fuwei007/NavBot-EG02/1-3D Files/1.jpg

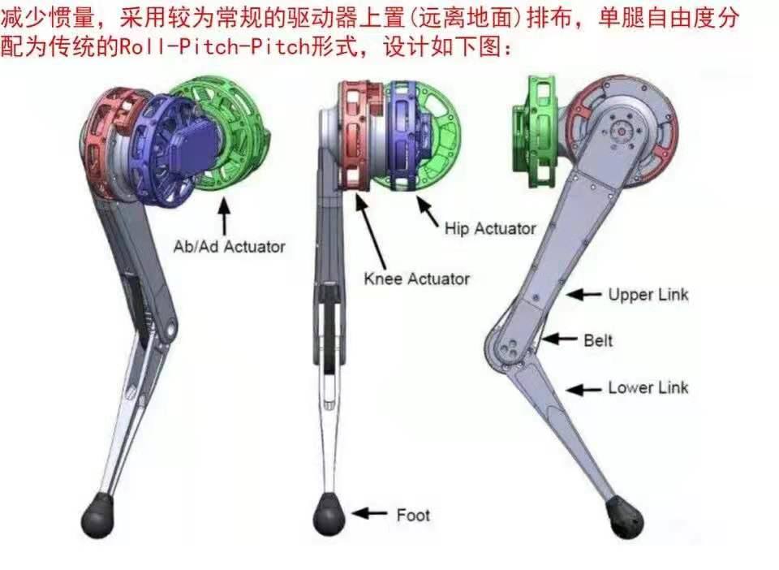
1-3D Files/1.jpg
