fuwei007/NavBot-EG02/1-3D Files/sw2022/MIT-机器狗-旋转关节.SLDASM

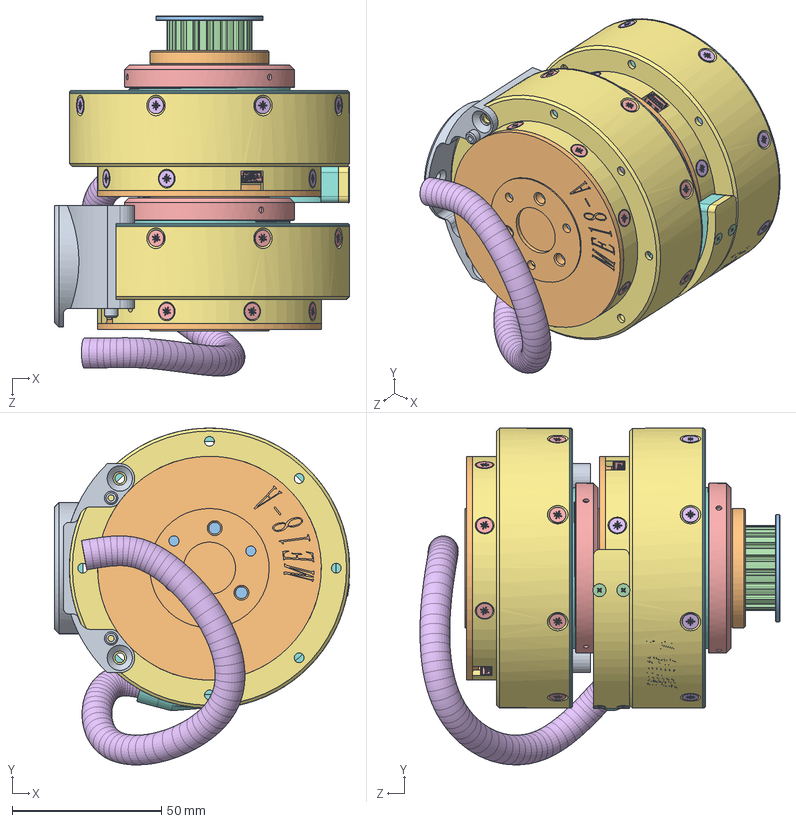
[picture p11: CAD file, 2025-09-24]
1-3D Files/sw2022/MIT-机器狗-旋转关节.SLDASM
99.0 x 112.9 x 120.7 mm
Smart Engines.sldasm-Part-1
Smart Engines.sldasm-Part-2 x 3
Smart Engines.sldasm-Part-4 x 2
Smart Engines.sldasm-Part-5 x 4
Smart Engines.sldasm-Part-6 x 13
Smart Engines.sldasm-Part-7
Smart Engines.sldasm-Part-8
Smart Engines.sldasm-Part-9 x 6
Smart Engines.sldasm-Part-10 x 2
3_BODY
Smart Engines.sldasm-Part-11 x 2
Smart Engines.sldasm-Part-12 x 2
Smart Engines.sldasm-Part-13 x 2
Smart Engines.sldasm-Part-14 x 2
Smart Engines.sldasm-Part-15 x 2
Smart Engines.sldasm-Part-16 x 2
Smart Engines.sldasm-Part-95
Smart Engines.sldasm-Part-96
GEAR_2_BODY
Smart Engines.sldasm-Part-105 x 13
Smart Engines.sldasm-Part-110
Smart Engines.sldasm-Part-114 x 2
Smart Engines.sldasm-Part-115 x 2
Smart Engines.sldasm-Part-116 x 2
Smart Engines.sldasm-Part-117 x 2
Smart Engines.sldasm-Part-118 x 2
Smart Engines.sldasm-Part-119 x 2
Smart Engines.sldasm-Part-120 x 2
Smart Engines.sldasm-Part-121 x 2
Smart Engines.sldasm-Part-122 x 2
