fuwei007/NavBot-EG02/1-3D Files/sw2022/Smart Engines.sldasm-Part-19.SLDPRT

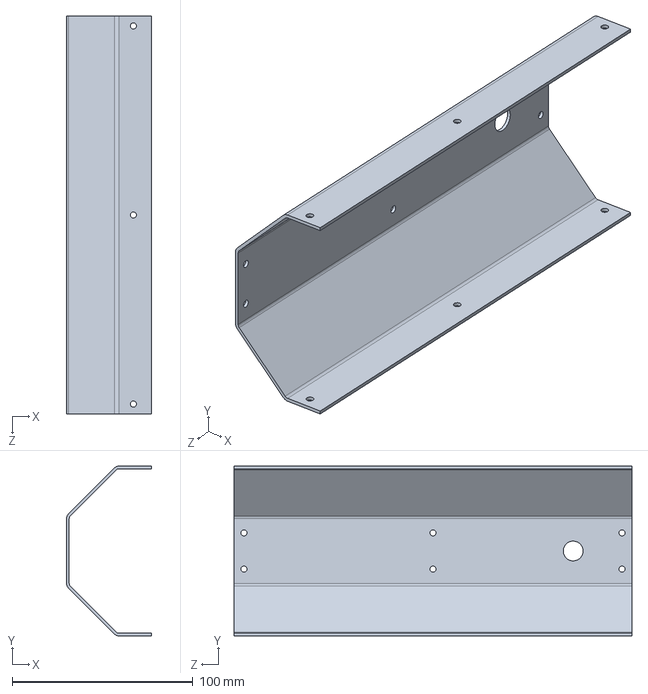
[picture p12: CAD file, 2025-09-24]
1-3D Files/sw2022/Smart Engines.sldasm-Part-19.SLDPRT
47.0 x 93.9 x 220.0 mm
