fuwei007/NavBot-EG02/1-3D Files/sw2022/MIT-机器狗-身体部分.SLDASM

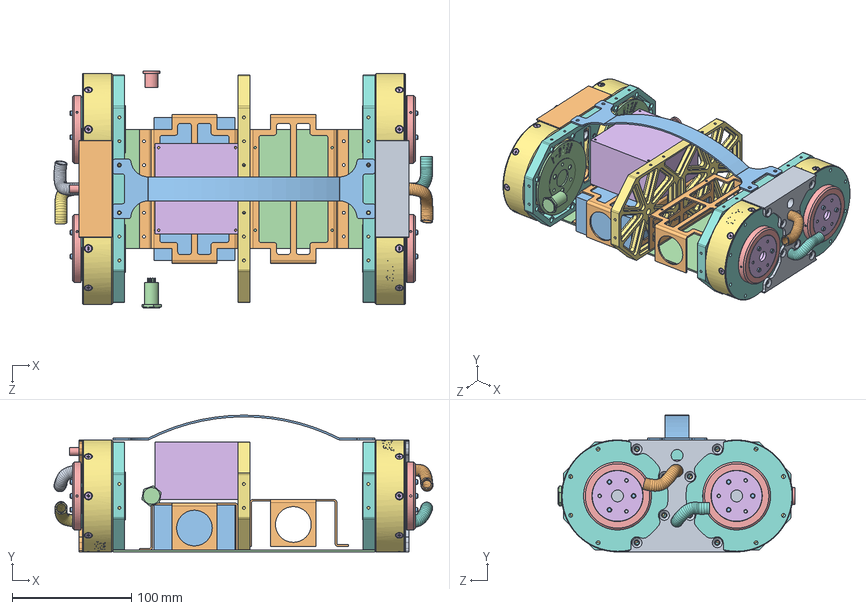
[picture p13: CAD file, 2025-09-24]
1-3D Files/sw2022/MIT-机器狗-身体部分.SLDASM
318.0 x 114.8 x 198.9 mm
Smart Engines.sldasm-Part-4 x 4
Smart Engines.sldasm-Part-9 x 12
Smart Engines.sldasm-Part-10 x 4
Smart Engines.sldasm-Part-12 x 4
Smart Engines.sldasm-Part-13 x 4
Smart Engines.sldasm-Part-14 x 4
Smart Engines.sldasm-Part-15 x 4
Smart Engines.sldasm-Part-16 x 4
Smart Engines.sldasm-Part-17 x 2
Smart Engines.sldasm-Part-18
Smart Engines.sldasm-Part-21
Smart Engines.sldasm-Part-22
Smart Engines.sldasm-Part-23
Smart Engines.sldasm-Part-24
Smart Engines.sldasm-Part-25 x 2
Smart Engines.sldasm-Part-26
Smart Engines.sldasm-Part-27
Smart Engines.sldasm-Part-28
Smart Engines.sldasm-Part-29
Smart Engines.sldasm-Part-30
Smart Engines.sldasm-Part-105 x 52
Smart Engines.sldasm-Part-107
Smart Engines.sldasm-Part-109
Smart Engines.sldasm-Part-111
Smart Engines.sldasm-Part-113
Smart Engines.sldasm-Part-114 x 4
Smart Engines.sldasm-Part-115 x 4
Smart Engines.sldasm-Part-116 x 4
Smart Engines.sldasm-Part-117 x 4
Smart Engines.sldasm-Part-118 x 4
Smart Engines.sldasm-Part-119 x 4
Smart Engines.sldasm-Part-120 x 4
Smart Engines.sldasm-Part-121 x 4
Smart Engines.sldasm-Part-122 x 4
