fuwei007/NavBot-EG02/1-3D Files/sw2022/Smart Engines.sldasm-Part-120.SLDPRT

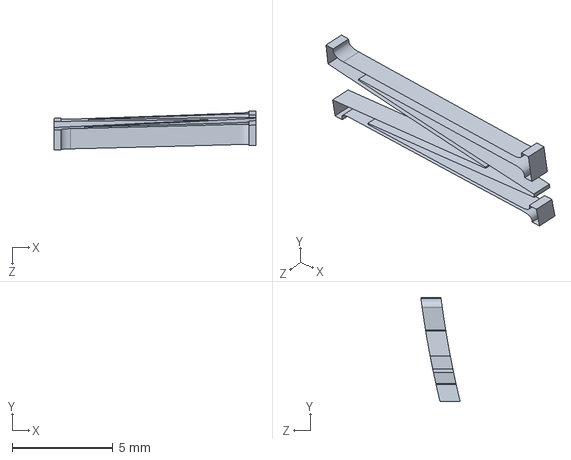
[picture p14: CAD file, 2025-09-24]
1-3D Files/sw2022/Smart Engines.sldasm-Part-120.SLDPRT
10.0 x 5.17 x 1.95 mm
