fuwei007/NavBot-EG02/3-Software/jetson_nano_-mit_-cheetah-main/resources/mini_body.obj

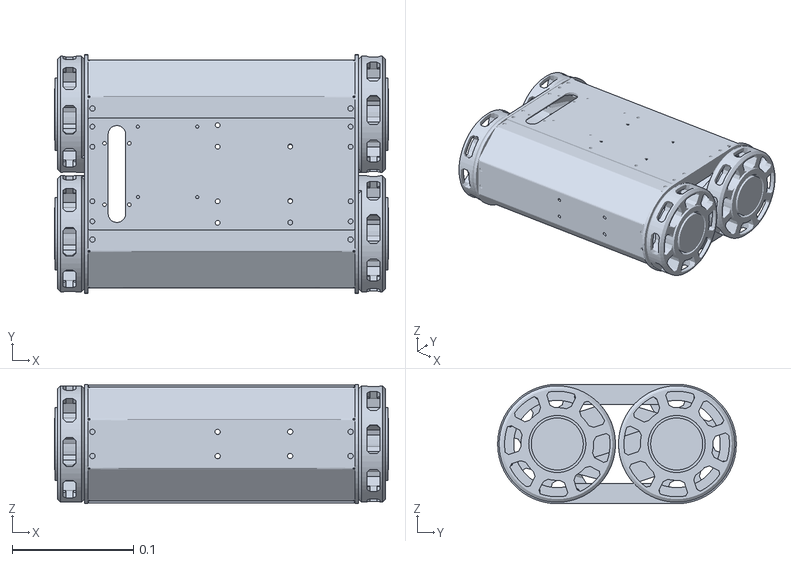
[picture p15: CAD file, 2025-09-24]
3-Software/jetson_nano_-mit_-cheetah-main/resources/mini_body.obj
0.275 x 0.197 x 0.0985
