fuwei007/NavBot-EG02/3-Software/jetson_nano_-mit_-cheetah-main/resources/sphere.obj

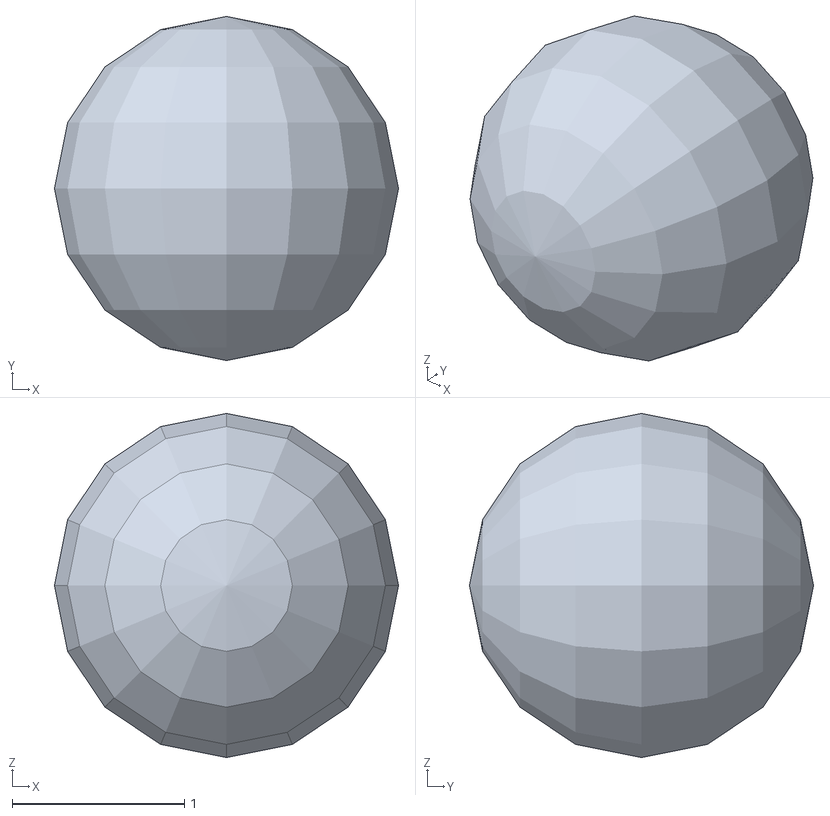
[picture p16: CAD file, 2025-09-24]
3-Software/jetson_nano_-mit_-cheetah-main/resources/sphere.obj
2.00 x 2.00 x 2.00
