fuwei007/NavBot-EG02/3-Software/jetson_nano_-mit_-cheetah-main/resources/mini_abad.obj

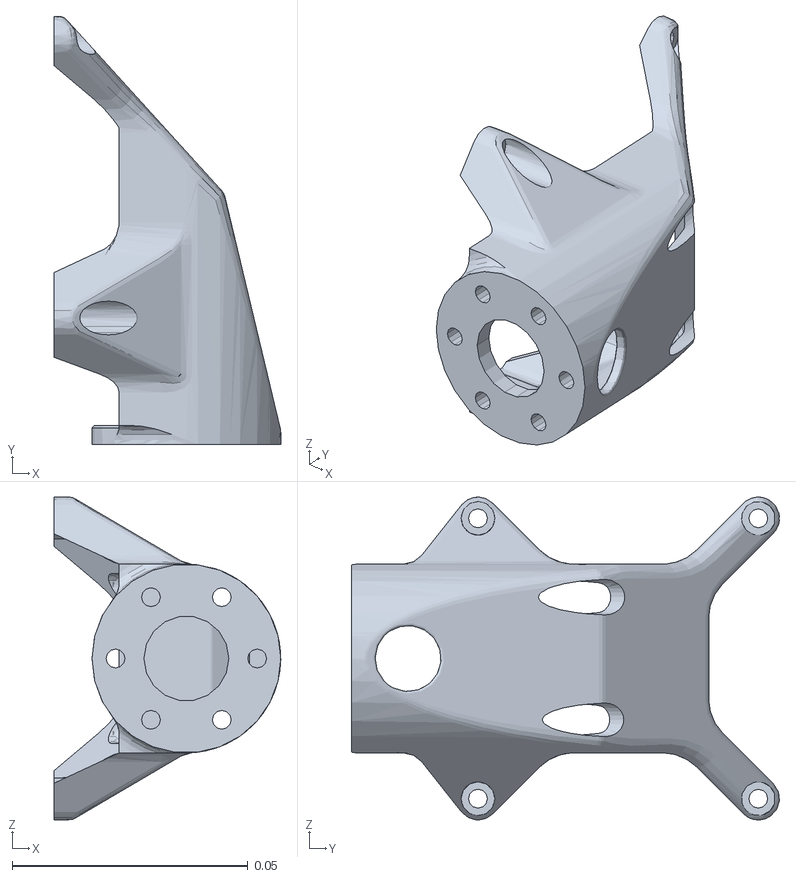
[picture p17: CAD file, 2025-09-24]
3-Software/jetson_nano_-mit_-cheetah-main/resources/mini_abad.obj
0.048 x 0.0907 x 0.0684
