fuwei007/NavBot-EG02/3-Software/jetson_nano_-mit_-cheetah-main/resources/mini_upper_link.obj

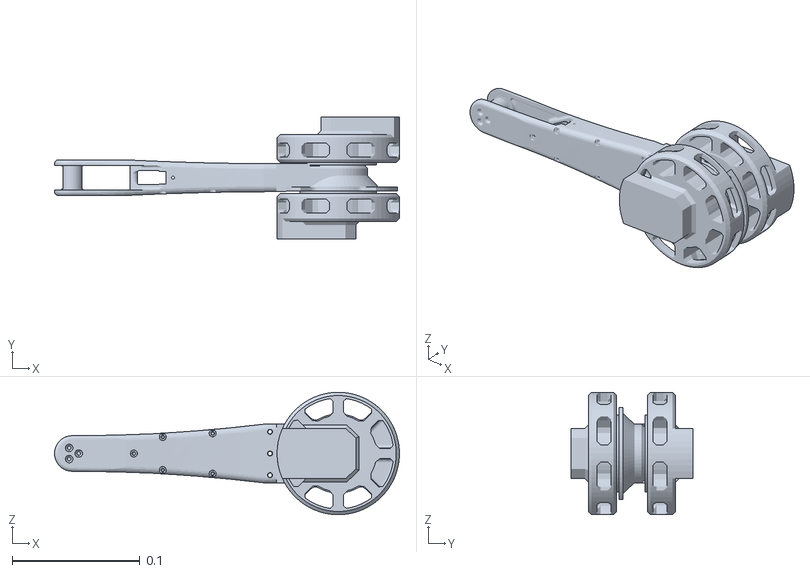
[picture p18: CAD file, 2025-09-24]
3-Software/jetson_nano_-mit_-cheetah-main/resources/mini_upper_link.obj
0.271 x 0.096 x 0.096
