fuwei007/NavBot-EG02/3-Software/jetson_nano_-mit_-cheetah-main/resources/c3_body.obj

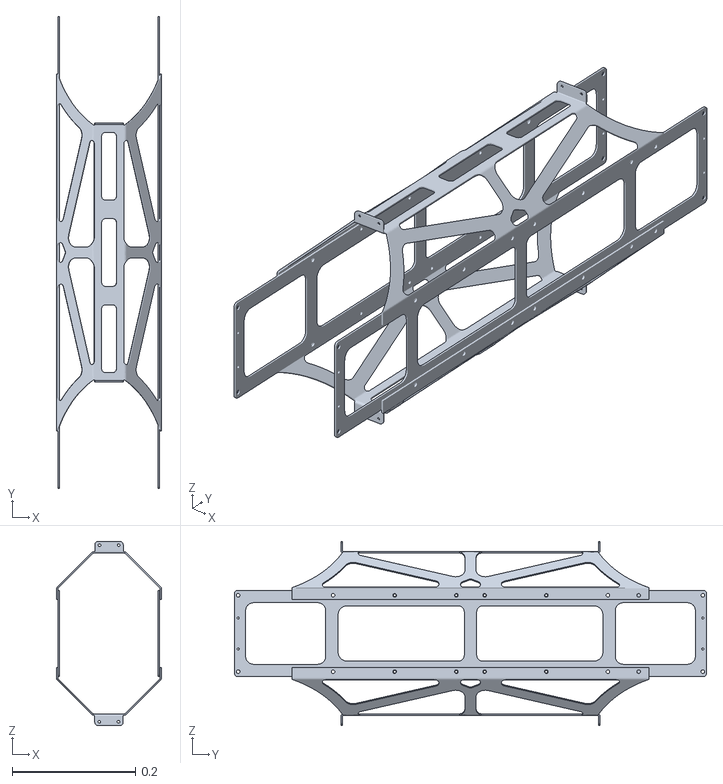
[picture p19: CAD file, 2025-09-24]
3-Software/jetson_nano_-mit_-cheetah-main/resources/c3_body.obj
0.171 x 0.766 x 0.299
