fuwei007/NavBot-EG02/3-Software/jetson_nano_-mit_-cheetah-main/resources/cube.obj

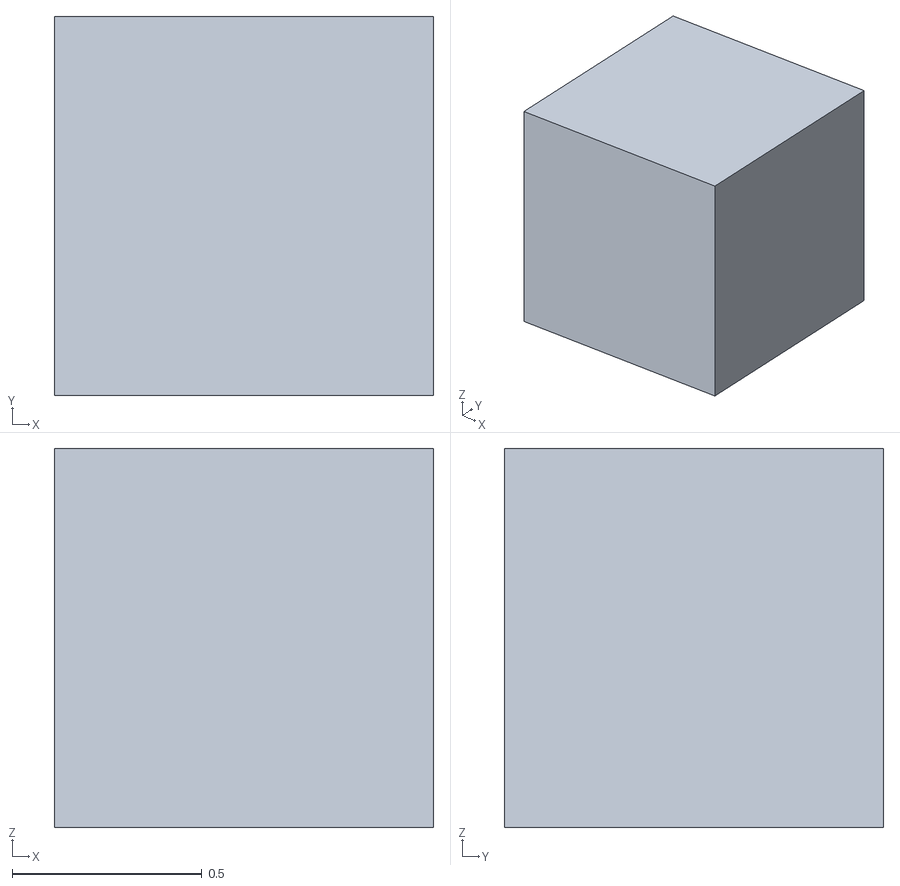
[picture p20: CAD file, 2025-09-24]
3-Software/jetson_nano_-mit_-cheetah-main/resources/cube.obj
1.00 x 1.00 x 1.00
