fuwei007/NavBot-EG02/3-Software/jetson_nano_-mit_-cheetah-main/resources/c3_upper_link.obj

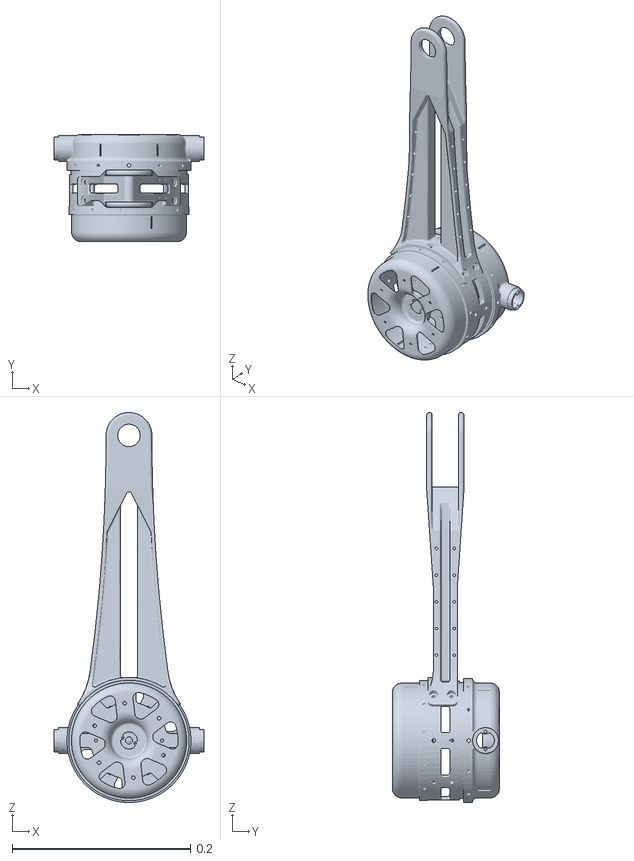
[picture p21: CAD file, 2025-09-24]
3-Software/jetson_nano_-mit_-cheetah-main/resources/c3_upper_link.obj
0.168 x 0.12 x 0.437
