fuwei007/NavBot-EG02/3-Software/jetson_nano_-mit_-cheetah-main/resources/mini_lower_link.obj

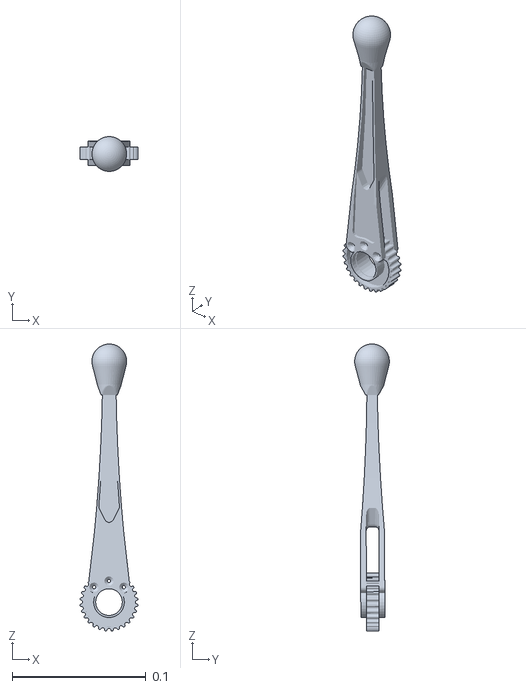
[picture p22: CAD file, 2025-09-24]
3-Software/jetson_nano_-mit_-cheetah-main/resources/mini_lower_link.obj
0.0432 x 0.026 x 0.215
