fuwei007/NavBot-EG02/3-Software/jetson_nano_-mit_-cheetah-main/resources/c3_lower_link.obj

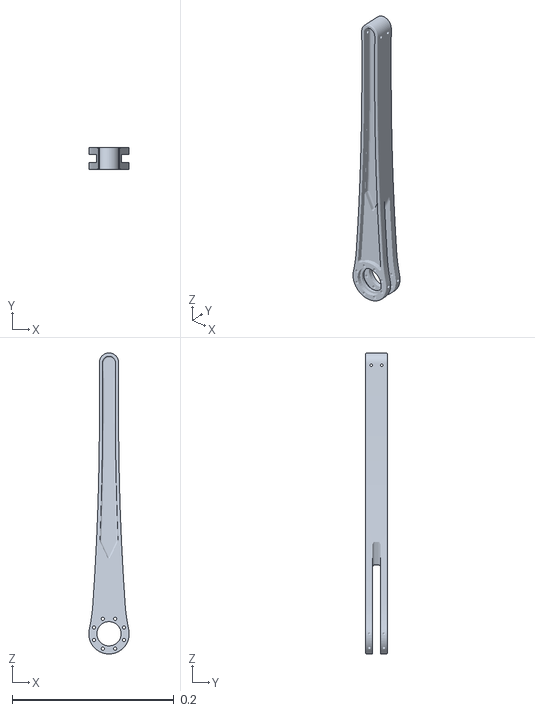
[picture p23: CAD file, 2025-09-24]
3-Software/jetson_nano_-mit_-cheetah-main/resources/c3_lower_link.obj
0.05 x 0.027 x 0.372
