fuwei007/NavBot-EG02/3-Software/jetson_nano_-mit_-cheetah-main/robot/src/RobotRunner.cpp

/*!
 * @file RobotRunner.cpp
 * @brief Common framework for running robot controllers.
 * This code is a common interface between control code and hardware/simulation
 * for mini cheetah and cheetah 3
 */

#include <unistd.h>

#include "RobotRunner.h"
#include "Controllers/ContactEstimator.h"
#include "Controllers/OrientationEstimator.h"
#include "Dynamics/Cheetah3.h"
#include "Dynamics/MiniCheetah.h"
#include "Utilities/Utilities_print.h"
#include "ParamHandler.hpp"
#include "Utilities/Timer.h"
#include "Controllers/PositionVelocityEstimator.h"
#include "user/MIT_Controller/FSM_States/FSM_State.h"
#include "Utilities/Log.h"
//#include "rt/rt_interface_lcm.h"

RobotRunner::RobotRunner(RobotController* robot_ctrl, 
    PeriodicTaskManager* manager, 
    float period, std::string name):
  PeriodicTask(manager, period, name),
  _lcm(getLcmUrl(255)) {

    _robot_ctrl = robot_ctrl;
  }

/**
 * Initializes the robot model, state estimator, leg controller,
 * robot data, and any control logic specific data.
 */
void RobotRunner::init() {
  LOG_INFO("[RobotRunner] initialize");

  // Build the appropriate Quadruped object
  if (robotType == RobotType::MINI_CHEETAH) {
    _quadruped = buildMiniCheetah<float>();
  } else {
    _quadruped = buildCheetah3<float>();
  }

  // Initialize the model and robot data
  _model = _quadruped.buildModel();
  _jpos_initializer = new JPosInitializer<float>(3., controlParameters->controller_dt);

  // Always initialize the leg controller and state entimator
  _legController = new LegController<float>(_quadruped);
  _stateEstimator = new StateEstimatorContainer<float>(
      cheaterState, vectorNavData, _legController->datas,
      &_stateEstimate, controlParameters);
  initializeStateEstimator(false);

  memset(&rc_control, 0, sizeof(rc_control_settings));
  // Initialize the DesiredStateCommand object
  _desiredStateCommand =
    new DesiredStateCommand<float>(driverCommand,
        &rc_control,
        controlParameters,
        &_stateEstimate,
        controlParameters->controller_dt);

  // Controller initializations
  _robot_ctrl->_model = &_model;
  _robot_ctrl->_quadruped = &_quadruped;
  _robot_ctrl->_legController = _legController;
  _robot_ctrl->_stateEstimator = _stateEstimator;
  _robot_ctrl->_stateEstimate = &_stateEstimate;
  _robot_ctrl->_visualizationData= visualizationData;
  _robot_ctrl->_robotType = robotType;
  _robot_ctrl->_driverCommand = driverCommand;
  _robot_ctrl->_controlParameters = controlParameters;
  _robot_ctrl->_desiredStateCommand = _desiredStateCommand;

  _robot_ctrl->initializeController();

  _gamepadPrevStart = false;
  _gamepadPrevBack = false;
  _gamepadPrevY = false;
  _gamepadPrevX = false;

}

/**
 * Runs the overall robot control system by calling each of the major components
 * to run each of their respective steps.
 */
void RobotRunner::run() {
  // Run the state estimator step
  //_stateEstimator->run(cheetahMainVisualization);
  _stateEstimator->run();
  //cheetahMainVisualization->p = _stateEstimate.position;
  visualizationData->clear();

  if (controlParameters && controlParameters->use_rc == 0 && driverCommand) {
    bool startPressed = driverCommand->start;
    bool backPressed = driverCommand->back;
    bool yPressed = driverCommand->y;
    bool xPressed = driverCommand->x;
    auto logButtonEdge = [&](const char* name, bool pressed) {
      LOG_WARN("[GAMEPAD] {} {}", name, pressed ? "pressed" : "released");
    };

    auto setMode = [&](int mode) {
      if (controlParameters->control_mode != static_cast<double>(mode)) {
        LOG_WARN("[GAMEPAD] control_mode {:.0f} -> {}",
                    controlParameters->control_mode, mode);
        controlParameters->control_mode = static_cast<double>(mode);
      }
    };

    if (startPressed != _gamepadPrevStart) {
      logButtonEdge("Start", startPressed);
    }
    if (yPressed != _gamepadPrevY) {
      logButtonEdge("Y", yPressed);
    }
    if (xPressed != _gamepadPrevX) {
      logButtonEdge("X", xPressed);
    }
    if (backPressed != _gamepadPrevBack) {
      logButtonEdge("Back", backPressed);
    }

    if (startPressed && !_gamepadPrevStart) {
      setMode(K_STAND_UP);
    }
    if (yPressed && !_gamepadPrevY) {
      setMode(K_LOCOMOTION);
    }
    if (xPressed && !_gamepadPrevX) {
      setMode(K_BALANCE_STAND);
    }
    if (backPressed && !_gamepadPrevBack) {
      setMode(K_PASSIVE);
    }

    _gamepadPrevStart = startPressed;
    _gamepadPrevBack = backPressed;
    _gamepadPrevY = yPressed;
    _gamepadPrevX = xPressed;
  }

  // Update the data from the robot
  setupStep();

  if (controlParameters && controlParameters->use_rc == 0 && driverCommand) {
    // [Gamepad -> RC Mapping]
    // Map gamepad sticks to rc_control for BalanceStand/Locomotion (MIT Standard Layout)
    rc_control.mode = controlParameters->control_mode; 
    
    // 灵敏度缩放系数
    const float kScaleRPY = 0.20f; // 最大 Roll/Pitch/Yaw 约 11.5 度 (更安全)
    const float kScaleH   = 0.3f;  // 降低高度调节幅度

    // 右摇杆: 姿态 (Roll/Pitch)
    rc_control.rpy_des[0] = driverCommand->rightStickAnalog[0] * kScaleRPY; // Roll = RX
    rc_control.rpy_des[1] = driverCommand->rightStickAnalog[1] * kScaleRPY; // Pitch = RY
    
    // 左摇杆: 偏航 & 高度 (Yaw & Height)
    rc_control.rpy_des[2] = -driverCommand->leftStickAnalog[0] * kScaleRPY; // Yaw = -LX
    rc_control.height_variation = driverCommand->leftStickAnalog[1] * kScaleH; // Height = LY

    // [DEBUG] Print Stick Values
    static int s_stick_log = 0;
    if (s_stick_log++ % 50 == 0) {
        LOG_INFO("[GAMEPAD] LX={:.3f} LY={:.3f} RX={:.3f} RY={:.3f}", 
                 (double)driverCommand->leftStickAnalog[0], (double)driverCommand->leftStickAnalog[1],
                 (double)driverCommand->rightStickAnalog[0], (double)driverCommand->rightStickAnalog[1]);
    }
  }

  static int count_ini(0);
  ++count_ini;
  if (count_ini < 10) {
    _legController->setEnabled(false);
  } else if (20 < count_ini && count_ini < 30) {
    _legController->setEnabled(false);
  } else if (40 < count_ini && count_ini < 50) {
    _legController->setEnabled(false);
  } else {
    _legController->setEnabled(true);

    if( (rc_control.mode == 0) && controlParameters->use_rc ) {
      if(count_ini%1000 ==0)   LOG_WARN("ESTOP!");
      for (int leg = 0; leg < 4; leg++) {
        _legController->commands[leg].zero();
      }
      _robot_ctrl->Estop();
    }else {
      // Controller
      if (!_jpos_initializer->IsInitialized(_legController)) {
        Mat3<float> kpMat;
        Mat3<float> kdMat;
        // Update the jpos feedback gains
        if (robotType == RobotType::MINI_CHEETAH) {
          kpMat << 5, 0, 0, 0, 5, 0, 0, 0, 5;
          kdMat << 0.1, 0, 0, 0, 0.1, 0, 0, 0, 0.1;
        } else if (robotType == RobotType::CHEETAH_3) {
          kpMat << 50, 0, 0, 0, 50, 0, 0, 0, 50;
          kdMat << 1, 0, 0, 0, 1, 0, 0, 0, 1;
        } else {
          assert(false);
        } 

        for (int leg = 0; leg < 4; leg++) {
          _legController->commands[leg].kpJoint = kpMat;
          _legController->commands[leg].kdJoint = kdMat;
        }
      } else {
        // Run Control 
        _robot_ctrl->runController();
        cheetahMainVisualization->p = _stateEstimate.position;

        // Update Visualization
        _robot_ctrl->updateVisualization();
        cheetahMainVisualization->p = _stateEstimate.position;
      }
    }

  }



  // Visualization (will make this into a separate function later)
  for (int leg = 0; leg < 4; leg++) {
    for (int joint = 0; joint < 3; joint++) {
      cheetahMainVisualization->q[leg * 3 + joint] =
        _legController->datas[leg].q[joint];
    }
  }
  cheetahMainVisualization->p.setZero();
  cheetahMainVisualization->p = _stateEstimate.position;
  cheetahMainVisualization->quat = _stateEstimate.orientation;

  // Sets the leg controller commands for the robot appropriate commands
  finalizeStep();
}

/*!
 * Before running user code, setup the leg control and estimators
 */
void RobotRunner::setupStep() {
  // Update the leg data
  if (robotType == RobotType::MINI_CHEETAH) {
    _legController->updateData(spiData);
  } else if (robotType == RobotType::CHEETAH_3) {
    _legController->updateData(tiBoardData);
  } else {
    assert(false);
  }

  // Setup the leg controller for a new iteration
  _legController->zeroCommand();
  _legController->setEnabled(true);
  _legController->setMaxTorqueCheetah3(208.5);

  // state estimator
  // check transition to cheater mode:
  if (!_cheaterModeEnabled && controlParameters->cheater_mode) {
    LOG_INFO("[RobotRunner] Transitioning to Cheater Mode...");
    initializeStateEstimator(true);
    // todo any configuration
    _cheaterModeEnabled = true;
  }

  // check transition from cheater mode:
  if (_cheaterModeEnabled && !controlParameters->cheater_mode) {
    LOG_INFO("[RobotRunner] Transitioning from Cheater Mode...");
    initializeStateEstimator(false);
    // todo any configuration
    _cheaterModeEnabled = false;
  }

  get_rc_control_settings(&rc_control);

  // todo safety checks, sanity checks, etc...
}

/*!
 * After the user code, send leg commands, update state estimate, and publish debug data
 */
void RobotRunner::finalizeStep() {
  if (robotType == RobotType::MINI_CHEETAH) {
    _legController->updateCommand(spiCommand);
  } else if (robotType == RobotType::CHEETAH_3) {
    _legController->updateCommand(tiBoardCommand);
  } else {
    assert(false);
  }
  _legController->setLcm(&leg_control_data_lcm, &leg_control_command_lcm);
  _stateEstimate.setLcm(state_estimator_lcm);
  _lcm.publish("leg_control_command", &leg_control_command_lcm);
  _lcm.publish("leg_control_data", &leg_control_data_lcm);
  _lcm.publish("state_estimator", &state_estimator_lcm);
  _iterations++;
}

/*!
 * Reset the state estimator in the given mode.
 * @param cheaterMode
 */
void RobotRunner::initializeStateEstimator(bool cheaterMode) {
  _stateEstimator->removeAllEstimators();
  _stateEstimator->addEstimator<ContactEstimator<float>>();
  Vec4<float> contactDefault;
  contactDefault << 0.5, 0.5, 0.5, 0.5;
  _stateEstimator->setContactPhase(contactDefault);
  if (cheaterMode) {
    _stateEstimator->addEstimator<CheaterOrientationEstimator<float>>();
    _stateEstimator->addEstimator<CheaterPositionVelocityEstimator<float>>();
  } else {
    _stateEstimator->addEstimator<VectorNavOrientationEstimator<float>>();
    _stateEstimator->addEstimator<LinearKFPositionVelocityEstimator<float>>();
  }
}

RobotRunner::~RobotRunner() {
  delete _legController;
  delete _stateEstimator;
  delete _jpos_initializer;
}

void RobotRunner::cleanup() {}
