fuwei007/NavBot-EG02/3-Software/jetson_nano_-mit_-cheetah-main/robot/include/HardwareBridge.h

/*!
 * @file HardwareBridge.h
 * @brief Interface between robot code and robot hardware
 *
 * This class initializes the hardware of both robots and allows the robot
 * controller to access it
 */

#ifndef PROJECT_HARDWAREBRIDGE_H
#define PROJECT_HARDWAREBRIDGE_H

#ifdef linux 

#define MAX_STACK_SIZE 16384  // 16KB  of stack
#define TASK_PRIORITY 49      // linux priority, this is not the nice value

#include <cstring>
#include <string>
#include <lcm-cpp.hpp>
#include "SimUtilities/LinuxGamepad.h"
#include "WheeltecImu.h"

#include "RobotRunner.h"
#include "Utilities/PeriodicTask.h"
#include "control_parameter_request_lcmt.hpp"
#include "control_parameter_respones_lcmt.hpp"
#include "gamepad_lcmt.hpp"
#include "microstrain_lcmt.hpp"
#include "ecat_command_t.hpp"
#include "ecat_data_t.hpp"



/*!
 * Interface between robot and hardware
 */
class HardwareBridge {
 public:
  HardwareBridge(RobotController* robot_ctrl)
      : statusTask(&taskManager, 0.5f),
        _interfaceLCM(getLcmUrl(255)),
        _visualizationLCM(getLcmUrl(255)) {
    _controller = robot_ctrl;
    _userControlParameters = robot_ctrl->getUserControlParameters();
    std::memset(&_parameter_response_lcmt, 0,
                sizeof(_parameter_response_lcmt));
        }
  void prefaultStack();
  void setupScheduler();
  void initError(const char* reason, bool printErrno = false);
  void initCommon();
  ~HardwareBridge() { delete _robotRunner; }
  void handleGamepadLCM(const lcm::ReceiveBuffer* rbuf, const std::string& chan,
                        const gamepad_lcmt* msg);

  void handleInterfaceLCM();
  void handleControlParameter(const lcm::ReceiveBuffer* rbuf,
                              const std::string& chan,
                              const control_parameter_request_lcmt* msg);

  void publishVisualizationLCM();
  void run_sbus();

 protected:
  PeriodicTaskManager taskManager;
  PrintTaskStatus statusTask;
  GamepadCommand _gamepadCommand;
  VisualizationData _visualizationData;
  CheetahVisualization _mainCheetahVisualization;
  lcm::LCM _interfaceLCM;
  lcm::LCM _visualizationLCM;
  control_parameter_respones_lcmt _parameter_response_lcmt;
  SpiData _spiData;
  SpiCommand _spiCommand;

  TiBoardCommand _tiBoardCommand[4];
  TiBoardData _tiBoardData[4];

  bool _firstRun = true;
  RobotRunner* _robotRunner = nullptr;
  RobotControlParameters _robotParams;
  u64 _iterations = 0;
  std::thread _interfaceLcmThread;
  volatile bool _interfaceLcmQuit = false;
  RobotController* _controller = nullptr;
  ControlParameters* _userControlParameters = nullptr;

  int _port;
};

/*!
 * Interface between robot and hardware specialized for Mini Cheetah
 */
class MiniCheetahHardwareBridge : public HardwareBridge {
 public:
  MiniCheetahHardwareBridge(RobotController* rc, bool load_parameters_from_file);
  void runSpi();
  void initHardware();
  void run();
  void runImu();
  void runGamepad();
  void logImu();
  void abort(const std::string& reason);
  void abort(const char* reason);

 private:
  VectorNavData _vectorNavData;
  lcm::LCM _spiLcm;
  lcm::LCM _imuLcm;
  std::thread _imuThread;
  std::thread _gamepadThread;
  WheeltecImu _wheeltecImu;
  LinuxGamepad _linuxGamepad;
  microstrain_lcmt _imuData;
  bool _imuInit = false;
  bool _gamepadInit = false;
  std::string _gamepadDevice;
  bool _load_parameters_from_file;
};

class Cheetah3HardwareBridge : public HardwareBridge {
public:
  Cheetah3HardwareBridge(RobotController* rc);
  void runEcat();
  void initHardware();
  void run();
  void publishEcatLCM();
  // todo imu?

private:
  VectorNavData _vectorNavData;
  lcm::LCM _ecatLCM;
  ecat_command_t ecatCmdLcm;
  ecat_data_t ecatDataLcm;
  // nothing?
};
#endif // END of #ifdef linux
#endif  // PROJECT_HARDWAREBRIDGE_H
