fuwei007/NavBot-EG02/3-Software/jetson_nano_-mit_-cheetah-main/common/src/Dynamics/Quadruped.cpp

/*! @file Quadruped.cpp
 *  @brief Data structure containing parameters for quadruped robot
 *
 *  This file contains the Quadruped class.  This stores all the parameters for
 * a quadruped robot.  There are utility functions to generate Quadruped objects
 * for Cheetah 3 (and eventually mini-cheetah). There is a buildModel() method
 * which can be used to create a floating-base dynamics model of the quadruped.
 */

#include "Dynamics/Quadruped.h"
#include "Dynamics/spatial.h"
#include "Math/orientation_tools.h"
#include "Utilities/Log.h"

using namespace ori;
using namespace spatial;

/*!
 * Build a FloatingBaseModel of the quadruped
 */
template <typename T>
bool Quadruped<T>::buildModel(FloatingBaseModel<T>& model) {
  static bool s_printed_params = false;
  if (!s_printed_params) {
     LOG_INFO("[Quadruped] Building Model with params: BodyMass={:.3f} AbadL={:.3f} HipL={:.3f} KneeL={:.3f} KneeYOff={:.3f}",
              (double)_bodyMass, (double)_abadLinkLength, (double)_hipLinkLength, (double)_kneeLinkLength, (double)_kneeLinkY_offset);
     s_printed_params = true;
  }

  // we assume the cheetah's body (not including rotors) can be modeled as a
  // uniformly distributed box.
  Vec3<T> bodyDims(_bodyLength, _bodyWidth, _bodyHeight);
  // model.addBase(_bodyMass, Vec3<T>(0,0,0), rotInertiaOfBox(_bodyMass,
  // bodyDims));
  model.addBase(_bodyInertia);
  // add contact for the cheetah's body
  model.addGroundContactBoxPoints(5, bodyDims);

  const int baseID = 5;
  int bodyID = baseID;
  T sideSign = -1;

  Mat3<T> I3 = Mat3<T>::Identity();

  // loop over 4 legs
  for (int legID = 0; legID < 4; legID++) {
    // Ab/Ad joint
    //  int addBody(const SpatialInertia<T>& inertia, const SpatialInertia<T>&
    //  rotorInertia, T gearRatio,
    //              int parent, JointType jointType, CoordinateAxis jointAxis,
    //              const Mat6<T>& Xtree, const Mat6<T>& Xrot);
    bodyID++;
    Mat6<T> xtreeAbad = createSXform(I3, withLegSigns<T>(_abadLocation, legID));
    Mat6<T> xtreeAbadRotor =
        createSXform(I3, withLegSigns<T>(_abadRotorLocation, legID));

    if (sideSign < 0) {
      model.addBody(_abadInertia.flipAlongAxis(CoordinateAxis::Y),
                    _abadRotorInertia.flipAlongAxis(CoordinateAxis::Y),
                    _abadGearRatio, baseID, JointType::Revolute,
                    CoordinateAxis::X, xtreeAbad, xtreeAbadRotor);
    } else {
      model.addBody(_abadInertia, _abadRotorInertia, _abadGearRatio, baseID,
                    JointType::Revolute, CoordinateAxis::X, xtreeAbad,
                    xtreeAbadRotor);
    }

    // Hip Joint
    bodyID++;
    Mat6<T> xtreeHip =
        createSXform(coordinateRotation<T>(CoordinateAxis::Z, T(M_PI)),
                     withLegSigns<T>(_hipLocation, legID));
    Mat6<T> xtreeHipRotor =
        createSXform(coordinateRotation<T>(CoordinateAxis::Z, T(M_PI)),
                     withLegSigns<T>(_hipRotorLocation, legID));
    if (sideSign < 0) {
      model.addBody(_hipInertia.flipAlongAxis(CoordinateAxis::Y),
                    _hipRotorInertia.flipAlongAxis(CoordinateAxis::Y),
                    _hipGearRatio, bodyID - 1, JointType::Revolute,
                    CoordinateAxis::Y, xtreeHip, xtreeHipRotor);
    } else {
      model.addBody(_hipInertia, _hipRotorInertia, _hipGearRatio, bodyID - 1,
                    JointType::Revolute, CoordinateAxis::Y, xtreeHip,
                    xtreeHipRotor);
    }

    // add knee ground contact point
    model.addGroundContactPoint(bodyID, Vec3<T>(0, 0, -_hipLinkLength));

    // Knee Joint
    bodyID++;
    Mat6<T> xtreeKnee = createSXform(I3, _kneeLocation);
    Mat6<T> xtreeKneeRotor = createSXform(I3, _kneeRotorLocation);
    if (sideSign < 0) {
      model.addBody(_kneeInertia.flipAlongAxis(CoordinateAxis::Y),
                    _kneeRotorInertia.flipAlongAxis(CoordinateAxis::Y),
                    _kneeGearRatio, bodyID - 1, JointType::Revolute,
                    CoordinateAxis::Y, xtreeKnee, xtreeKneeRotor);

      model.addGroundContactPoint(bodyID, Vec3<T>(0, _kneeLinkY_offset, -_kneeLinkLength), true);
    } else {
      model.addBody(_kneeInertia, _kneeRotorInertia, _kneeGearRatio, bodyID - 1,
                    JointType::Revolute, CoordinateAxis::Y, xtreeKnee,
                    xtreeKneeRotor);

      model.addGroundContactPoint(bodyID, Vec3<T>(0, -_kneeLinkY_offset, -_kneeLinkLength), true);
    }

    // add foot
    //model.addGroundContactPoint(bodyID, Vec3<T>(0, 0, -_kneeLinkLength), true);

    sideSign *= -1;
  }

  Vec3<T> g(0, 0, -9.81);
  model.setGravity(g);

  return true;
}

/*!
 * Build a FloatingBaseModel of the quadruped
 */
template <typename T>
FloatingBaseModel<T> Quadruped<T>::buildModel() {
  FloatingBaseModel<T> model;
  buildModel(model);
/*
  // we assume the cheetah's body (not including rotors) can be modeled as a
  // uniformly distributed box.
  Vec3<T> bodyDims(_bodyLength, _bodyWidth, _bodyHeight);
  // model.addBase(_bodyMass, Vec3<T>(0,0,0), rotInertiaOfBox(_bodyMass,
  // bodyDims));
  model.addBase(_bodyInertia);
  // add contact for the cheetah's body
  model.addGroundContactBoxPoints(5, bodyDims);

  const int baseID = 5;
  int bodyID = baseID;
  T sideSign = -1;

  Mat3<T> I3 = Mat3<T>::Identity();

  // loop over 4 legs
  for (int legID = 0; legID < 4; legID++) {
    // Ab/Ad joint
    //  int addBody(const SpatialInertia<T>& inertia, const SpatialInertia<T>&
    //  rotorInertia, T gearRatio,
    //              int parent, JointType jointType, CoordinateAxis jointAxis,
    //              const Mat6<T>& Xtree, const Mat6<T>& Xrot);
    bodyID++;
    Mat6<T> xtreeAbad = createSXform(I3, withLegSigns<T>(_abadLocation, legID));
    Mat6<T> xtreeAbadRotor =
        createSXform(I3, withLegSigns<T>(_abadRotorLocation, legID));

    if (sideSign < 0) {
      model.addBody(_abadInertia.flipAlongAxis(CoordinateAxis::Y),
                    _abadRotorInertia.flipAlongAxis(CoordinateAxis::Y),
                    _abadGearRatio, baseID, JointType::Revolute,
                    CoordinateAxis::X, xtreeAbad, xtreeAbadRotor);
    } else {
      model.addBody(_abadInertia, _abadRotorInertia, _abadGearRatio, baseID,
                    JointType::Revolute, CoordinateAxis::X, xtreeAbad,
                    xtreeAbadRotor);
    }

    // Hip Joint
    bodyID++;
    Mat6<T> xtreeHip =
        createSXform(coordinateRotation<T>(CoordinateAxis::Z, T(M_PI)),
                     withLegSigns<T>(_hipLocation, legID));
    Mat6<T> xtreeHipRotor =
        createSXform(coordinateRotation<T>(CoordinateAxis::Z, T(M_PI)),
                     withLegSigns<T>(_hipRotorLocation, legID));
    if (sideSign < 0) {
      model.addBody(_hipInertia.flipAlongAxis(CoordinateAxis::Y),
                    _hipRotorInertia.flipAlongAxis(CoordinateAxis::Y),
                    _hipGearRatio, bodyID - 1, JointType::Revolute,
                    CoordinateAxis::Y, xtreeHip, xtreeHipRotor);
    } else {
      model.addBody(_hipInertia, _hipRotorInertia, _hipGearRatio, bodyID - 1,
                    JointType::Revolute, CoordinateAxis::Y, xtreeHip,
                    xtreeHipRotor);
    }

    // add knee ground contact point
    model.addGroundContactPoint(bodyID, Vec3<T>(0, 0, -_hipLinkLength));

    // Knee Joint
    bodyID++;
    Mat6<T> xtreeKnee = createSXform(I3, _kneeLocation);
    Mat6<T> xtreeKneeRotor = createSXform(I3, _kneeRotorLocation);
    if (sideSign < 0) {
      model.addBody(_kneeInertia.flipAlongAxis(CoordinateAxis::Y),
                    _kneeRotorInertia.flipAlongAxis(CoordinateAxis::Y),
                    _kneeGearRatio, bodyID - 1, JointType::Revolute,
                    CoordinateAxis::Y, xtreeKnee, xtreeKneeRotor);
    } else {
      model.addBody(_kneeInertia, _kneeRotorInertia, _kneeGearRatio, bodyID - 1,
                    JointType::Revolute, CoordinateAxis::Y, xtreeKnee,
                    xtreeKneeRotor);
    }

    // add foot
    model.addGroundContactPoint(bodyID, Vec3<T>(0, 0, -_kneeLinkLength), true);

    sideSign *= -1;
  }

  Vec3<T> g(0, 0, -9.81);
  model.setGravity(g);
*/
  return model;
}

/*!
 * Flip signs of elements of a vector V depending on which leg it belongs to
 */
template <typename T, typename T2>
Vec3<T> withLegSigns(const Eigen::MatrixBase<T2>& v, int legID) {
  static_assert(T2::ColsAtCompileTime == 1 && T2::RowsAtCompileTime == 3,
                "Must have 3x1 matrix");
  switch (legID) {
    case 0:
      return Vec3<T>(v[0], -v[1], v[2]);
    case 1:
      return Vec3<T>(v[0], v[1], v[2]);
    case 2:
      return Vec3<T>(-v[0], -v[1], v[2]);
    case 3:
      return Vec3<T>(-v[0], v[1], v[2]);
    default:
      throw std::runtime_error("Invalid leg id!");
  }
}

/*!
 * Build actuator models for a leg
 */
template <typename T>
std::vector<ActuatorModel<T>> Quadruped<T>::buildActuatorModels() {
  std::vector<ActuatorModel<T>> models;
  models.emplace_back(_abadGearRatio, _motorKT, _motorR, _batteryV,
                      _jointDamping, _jointDryFriction, _motorTauMax);
  models.emplace_back(_hipGearRatio, _motorKT, _motorR, _batteryV,
                      _jointDamping, _jointDryFriction, _motorTauMax);
  models.emplace_back(_kneeGearRatio, _motorKT, _motorR, _batteryV,
                      _jointDamping, _jointDryFriction, _motorTauMax);
  return models;
}

template class Quadruped<double>;
template class Quadruped<float>;
