fuwei007/NavBot-EG02/3-Software/jetson_nano_-mit_-cheetah-main/robot/include/SimulationBridge.h

/*! @file SimulationBridge.h
 *  @brief  The SimulationBridge runs a RobotController and connects it to a
 * Simulator, using shared memory. It is the simulation version of the
 * HardwareBridge.
 */

#ifndef PROJECT_SIMULATIONDRIVER_H
#define PROJECT_SIMULATIONDRIVER_H

#include <string>
#include <thread>

#include "ControlParameters/RobotParameters.h"
#include "RobotRunner.h"
#include "SimUtilities/LinuxGamepad.h"
#include "SimUtilities/SimulatorMessage.h"
#include "Types.h"
#include "Utilities/PeriodicTask.h"
#include "Utilities/SharedMemory.h"

class SimulationBridge {
 public:
  explicit SimulationBridge(RobotType robot, RobotController* robot_ctrl) : 
    _robot(robot) {
     _fakeTaskManager = new PeriodicTaskManager;
    _robotRunner = new RobotRunner(robot_ctrl, _fakeTaskManager, 0, "robot-task");
    _userParams = robot_ctrl->getUserControlParameters();

 }
  void run();
  void handleControlParameters();
  void runRobotControl();
  void runGamepad();
  ~SimulationBridge() {
    delete _fakeTaskManager;
    delete _robotRunner;
  }
 private:
  PeriodicTaskManager taskManager;
  bool _firstControllerRun = true;
  PeriodicTaskManager* _fakeTaskManager = nullptr;
  RobotType _robot;
  RobotRunner* _robotRunner = nullptr;
  SimulatorMode _simMode;
  SharedMemoryObject<SimulatorSyncronizedMessage> _sharedMemory;
  RobotControlParameters _robotParams;
  ControlParameters* _userParams = nullptr;
  u64 _iterations = 0;
  GamepadCommand _gamepadCommand;
  LinuxGamepad _linuxGamepad;
  bool _gamepadInit = false;
  std::string _gamepadDevice;
  std::thread _gamepadThread;

};

#endif  // PROJECT_SIMULATIONDRIVER_H
